rgalland/PC-Engine_CDR-30A_Schematics/Datasheets/cxa-1081S.gif

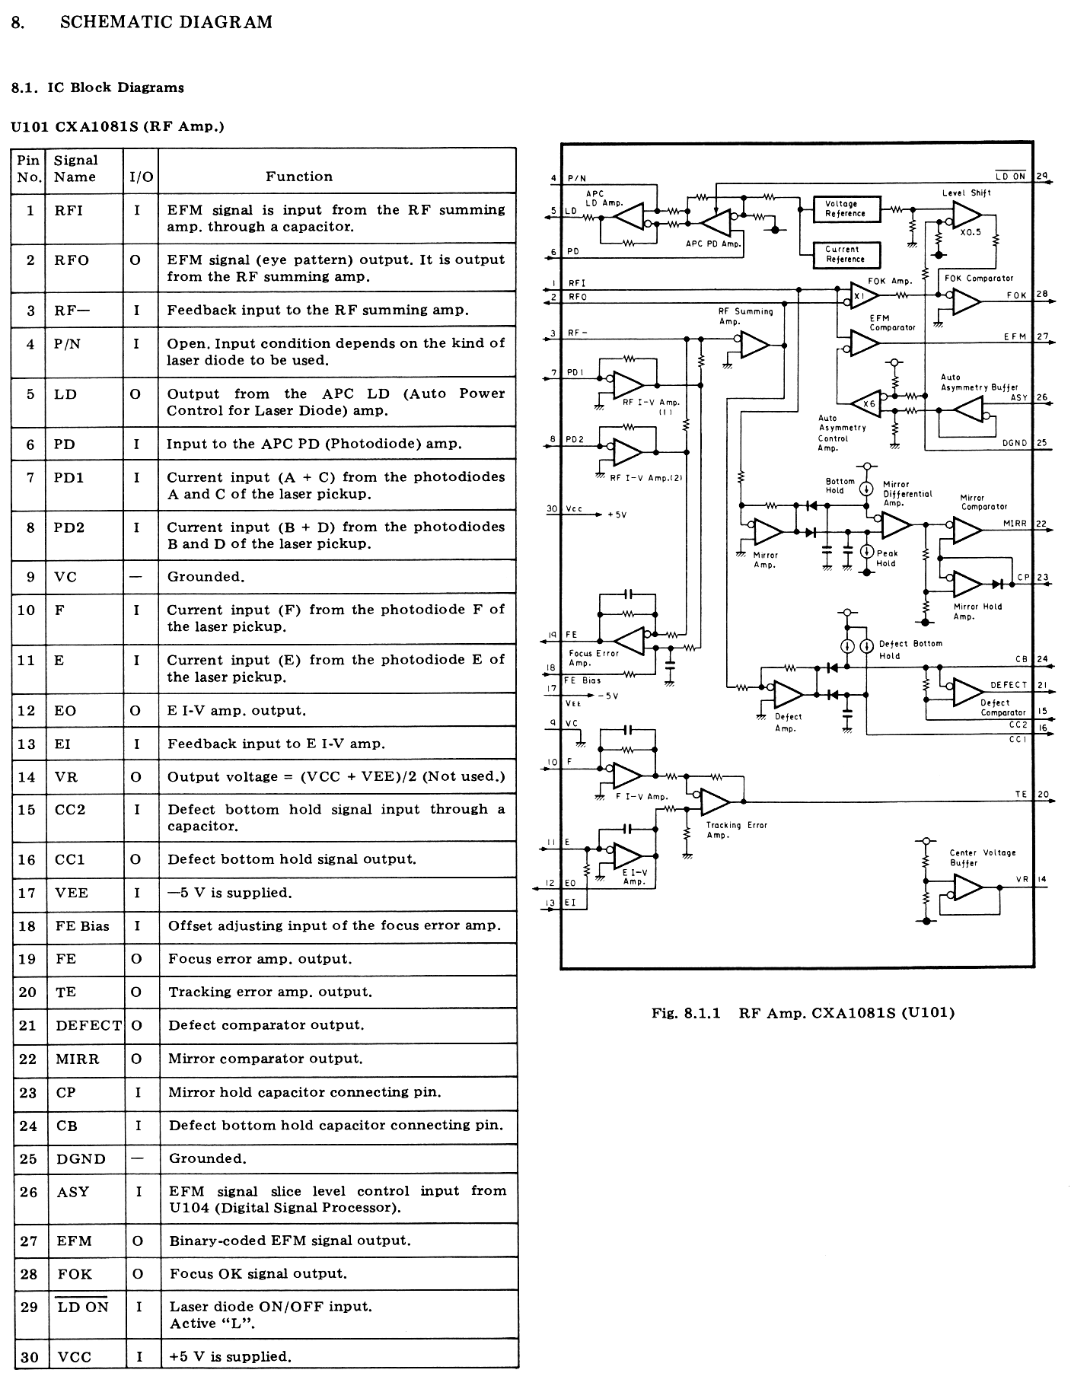
Datasheets/cxa-1081S.gif
