rgalland/PC-Engine_CDR-30A_Schematics/Datasheets/CXD1167/CXD1167-Pin-Functions-2.png

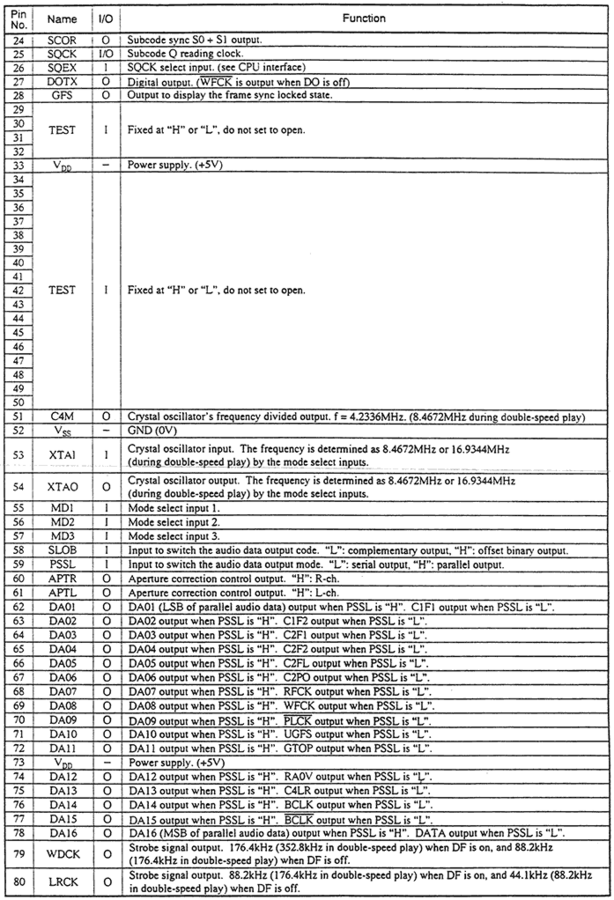
Datasheets/CXD1167/CXD1167-Pin-Functions-2.png
