rgalland/PC-Engine_CDR-30A_Schematics/Datasheets/Kyocera_connector.png

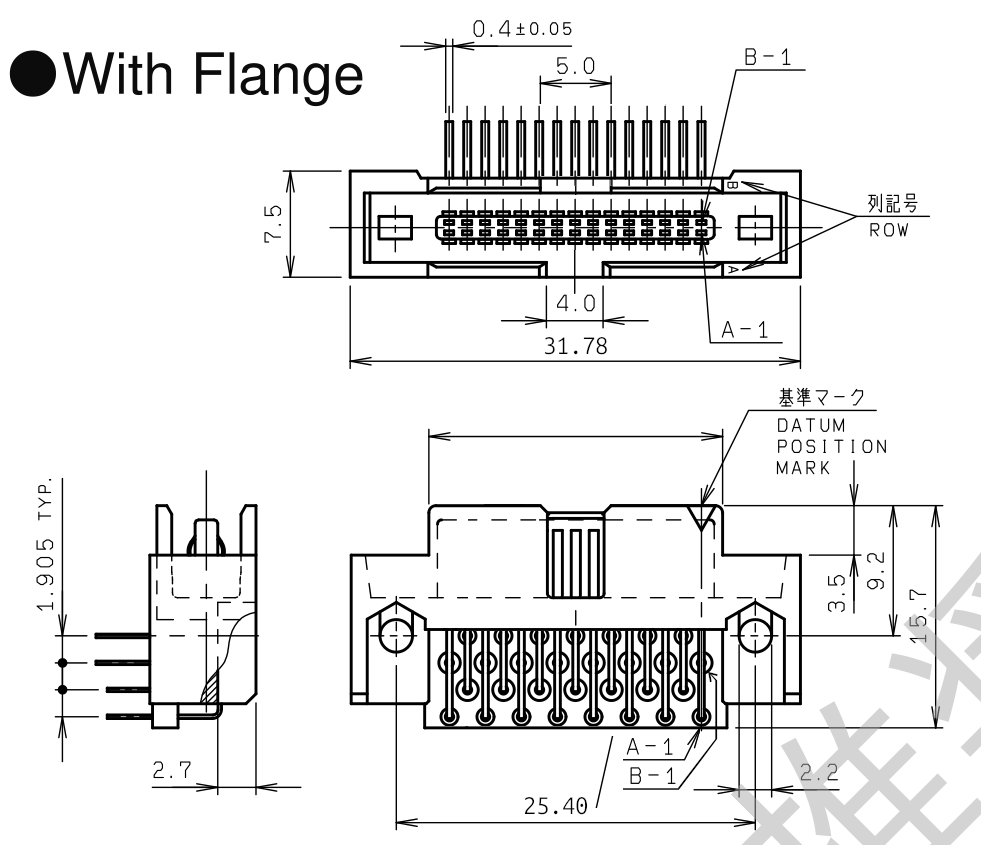
Datasheets/Kyocera_connector.png
