rgalland/PC-Engine_CDR-30A_Schematics/Original_PCBs/Focus_Tracking_Flex/Scanned_Focus_Tacking_Flex.png

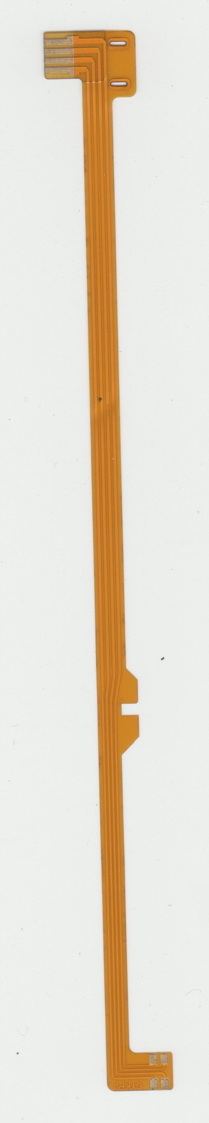
Original_PCBs/Focus_Tracking_Flex/Scanned_Focus_Tacking_Flex.png
