rgalland/PC-Engine_CDR-30A_Schematics/Original_PCBs/Lens_Flex/Ruban-de-c-ble-pour-t-te-laser-KSS-220A-2-pi-ces-12-broches-4.jpg

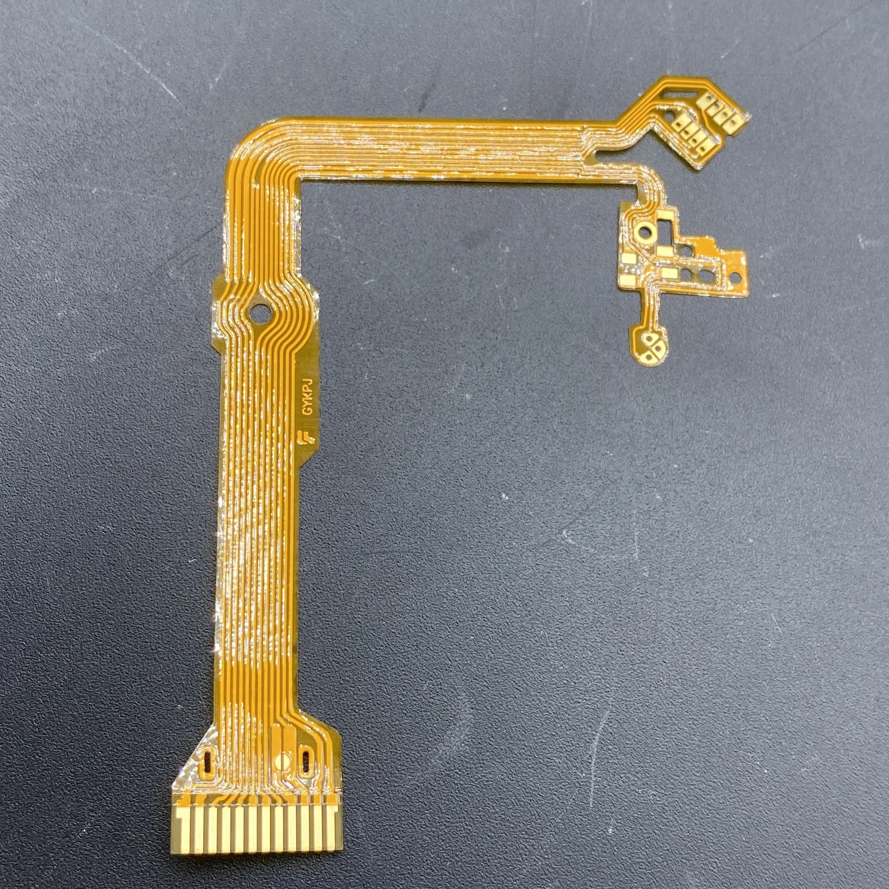
Original_PCBs/Lens_Flex/Ruban-de-c-ble-pour-t-te-laser-KSS-220A-2-pi-ces-12-broches-4.jpg
