rgalland/PC-Engine_CDR-30A_Schematics/Reproduction_PCBs/Main_PCB/Main_PCB_Top.png

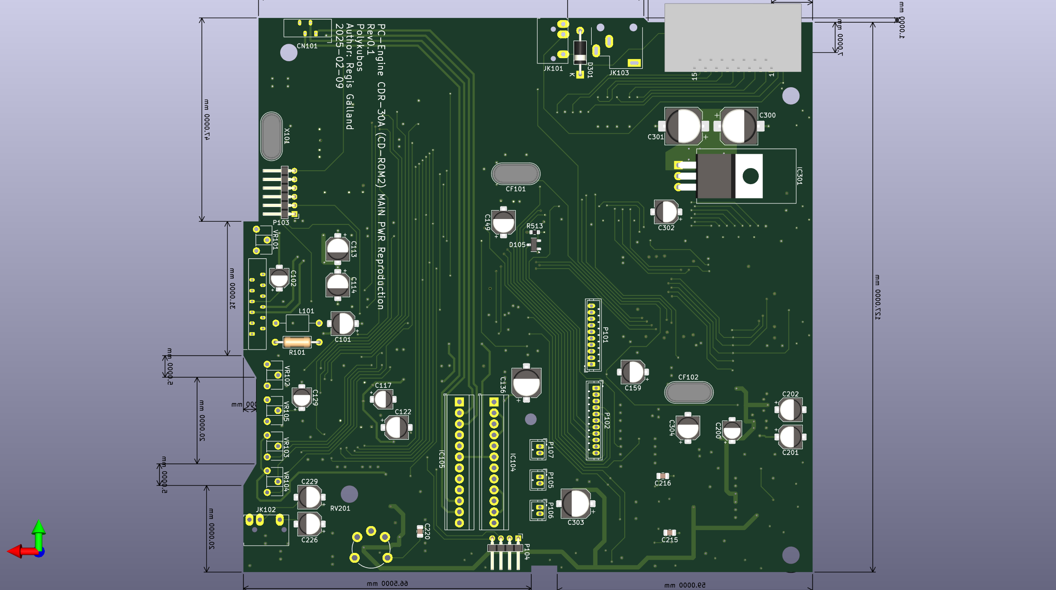
Reproduction_PCBs/Main_PCB/Main_PCB_Top.png
